bt-soft/pico-radio-5/doc/20250502_175417.jpg

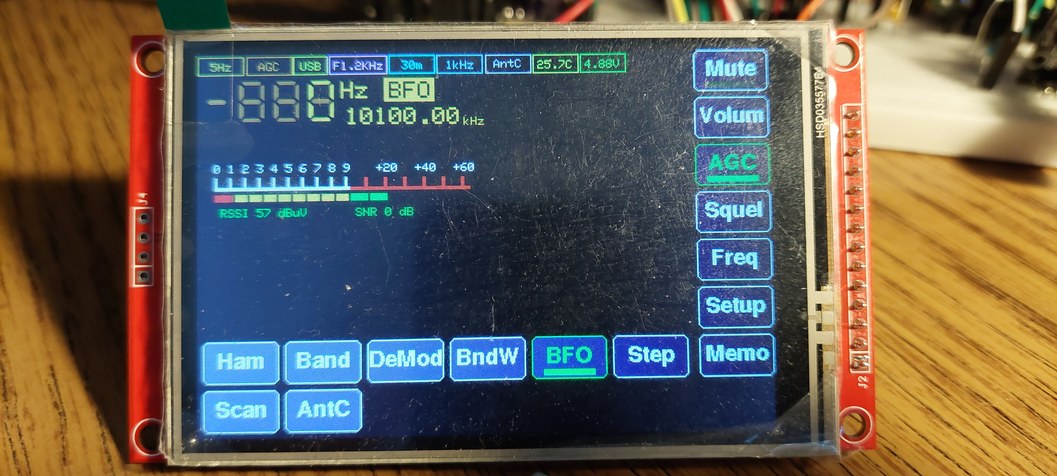
doc/20250502_175417.jpg
