bt-soft/pico-radio-5/doc/20250522_205130.jpg

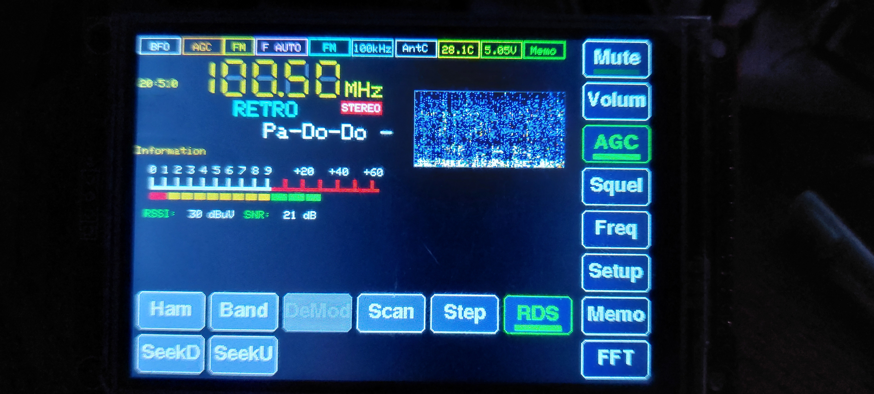
doc/20250522_205130.jpg
