bt-soft/pico-radio-5/doc/20250522_205135.jpg

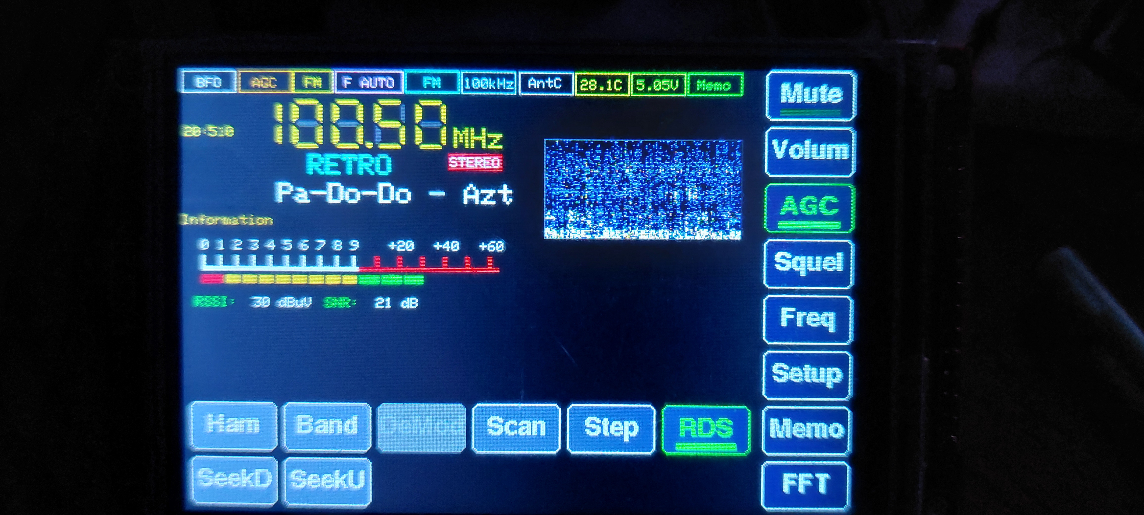
doc/20250522_205135.jpg
