bt-soft/pico-radio-5/doc/20250522_205156.jpg

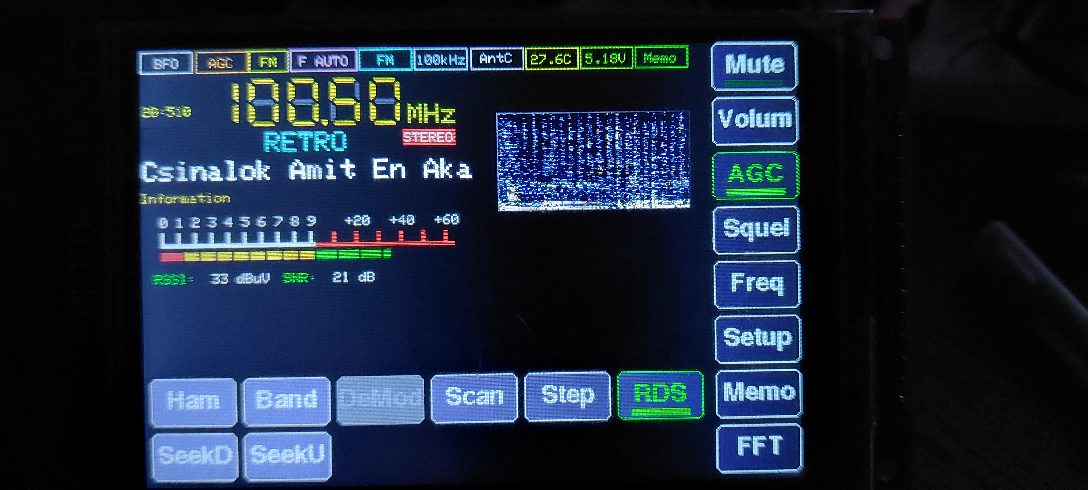
doc/20250522_205156.jpg
