bt-soft/pico-radio-5/doc/20250809_113343.jpg

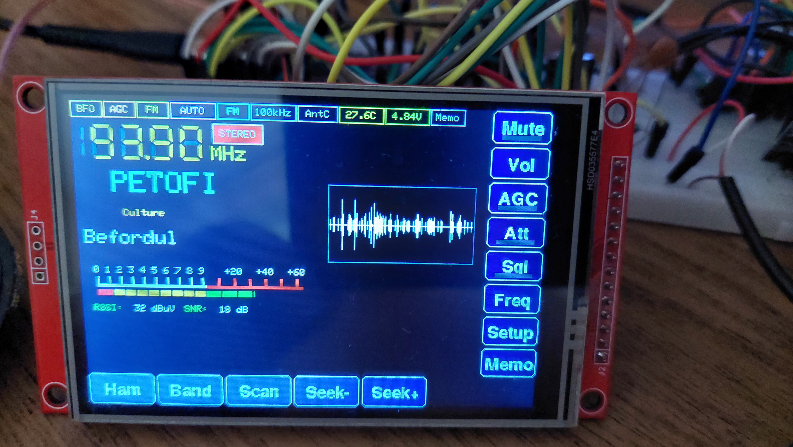
doc/20250809_113343.jpg
