bt-soft/pico-radio-5/include/DSEG7_Classic_Mini_Regular_34.h

// Created by http://oleddisplay.squix.ch/ Consider a donation
// In case of problems make sure that you are using the font file with the correct version!
const uint8_t DSEG7_Classic_Mini_Regular_34Bitmaps[] PROGMEM = {

    // Bitmap Data:
    0x00,                                                                                                                                                                         // ' '
    0x00,                                                                                                                                                                         // '!'
    0xFF, 0xA0, 0x28, 0x0A, 0x02, 0x80, 0xA0, 0x28, 0x0A, 0x02, 0x80, 0xA0, 0x28, 0x0A, 0x02, 0x80, 0xA0, 0x28, 0x0A, 0x02, 0x80, 0xA0, 0x28, 0x0A, 0x02, 0x80, 0xA0, 0x2F, 0xF8, // '"'
    0xFF, 0xA0, 0x28, 0x0A, 0x02, 0x80, 0xA0, 0x28, 0x0A, 0x02, 0x80, 0xA0, 0x28, 0x0A, 0x02, 0x80, 0xA0, 0x28, 0x0A, 0x02, 0x80, 0xA0, 0x28, 0x0A, 0x02, 0x80, 0xA0, 0x2F, 0xF8, // '#'
    0xFF, 0xA0, 0x28, 0x0A, 0x02, 0x80, 0xA0, 0x28, 0x0A, 0x02, 0x80, 0xA0, 0x28, 0x0A, 0x02, 0x80, 0xA0, 0x28, 0x0A, 0x02, 0x80, 0xA0, 0x28, 0x0A, 0x02, 0x80, 0xA0, 0x2F, 0xF8, // '$'
    0xFF, 0xA0, 0x28, 0x0A, 0x02, 0x80, 0xA0, 0x28, 0x0A, 0x02, 0x80, 0xA0, 0x28, 0x0A, 0x02, 0x80, 0xA0, 0x28, 0x0A, 0x02, 0x80, 0xA0, 0x28, 0x0A, 0x02, 0x80, 0xA0, 0x2F, 0xF8, // '%'
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
    {456, 4, 28, 29, 21, -31},  // '1'
    {470, 22, 34, 29, 3, -34},  // '2'
    {564, 19, 34, 29, 6, -34},  // '3'
    {645, 22, 28, 29, 3, -31},  // '4'
    {722, 22, 34, 29, 3, -34},  // '5'
    {816, 22, 34, 29, 3, -34},  // '6'
    {910, 22, 31, 29, 3, -34},  // '7'
    {996, 22, 34, 29, 3, -34},  // '8'
    {1090, 22, 34, 29, 3, -34}, // '9'
    {1184, 6, 19, 8, 1, -26},   // ':'
    {1199, 10, 23, 13, 1, -23}, // ';'
    {1228, 10, 23, 13, 1, -23}, // '<'
    {1257, 10, 23, 13, 1, -23}, // '='
    {1286, 10, 23, 13, 1, -23}, // '>'
    {1315, 10, 23, 13, 1, -23}, // '?'
    {1344, 10, 23, 13, 1, -23}, // '@'
    {1373, 22, 31, 29, 3, -34}, // 'A'
    {1459, 22, 31, 29, 3, -31}, // 'B'
    {1545, 20, 19, 29, 3, -19}, // 'C'
    {1593, 22, 31, 29, 3, -31}, // 'D'
    {1679, 20, 34, 29, 3, -34}, // 'E'
    {1764, 20, 31, 29, 3, -34}, // 'F'
    {1842, 22, 34, 29, 3, -34}, // 'G'
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
};
const GFXfont DSEG7_Classic_Mini_Regular_34 PROGMEM = {(uint8_t *)DSEG7_Classic_Mini_Regular_34Bitmaps, (GFXglyph *)DSEG7_Classic_Mini_Regular_34Glyphs, 0x20, 0x7E, 38};
