bt-soft/pico-radio-5/include/CommonVerticalButtons.h

#pragma once

#include "FrequencyInputDialog.h"
#include "ScreenRadioBase.h"
#include "Si4735Manager.h"
#include "UIButton.h"
#include "ValueChangeDialog.h"
#include "rtVars.h"

// ===================================================================
// UNIVERZÁLIS GOMB AZONOSÍTÓK - Egységes ID rendszer
// ===================================================================

namespace VerticalButtonIDs {
static constexpr uint8_t MUTE = 10;    ///< Némítás gomb (univerzális)
static constexpr uint8_t VOLUME = 11;  ///< Hangerő beállítás gomb (univerzális)
static constexpr uint8_t AGC = 12;     ///< Automatikus erősítés szabályozás (univerzális)
static constexpr uint8_t ATT = 13;     ///< Csillapító (univerzális)
static constexpr uint8_t SQUELCH = 14; ///< Zajzár beállítás (univerzális)
static constexpr uint8_t FREQ = 15;    ///< Frekvencia input (univerzális)
static constexpr uint8_t SETUP = 16;   ///< Beállítások képernyő (univerzális)
static constexpr uint8_t MEMO = 17;    ///< Memória funkciók (univerzális)
} // namespace VerticalButtonIDs

/**
 * @brief Közös függőleges gombsor statikus osztály dialógus támogatással
 * @details Handler függvények képesek dialógusokat megjeleníteni
 */
class CommonVerticalButtons {
  public:
    // =====================================================================
    // HANDLER FÜGGVÉNY TÍPUSOK - Egységes ScreenRadioBase alapú megközelítés
    // =====================================================================
    using HandlerFunc = void (*)(const UIButton::ButtonEvent &, ScreenRadioBase *);

    // Kompatibilitás miatt megtartjuk a régi neveket, de mind azonos típusra mutatnak
    using CommonHandlerFunc = HandlerFunc;
    using Si4735HandlerFunc = HandlerFunc;
    using DialogHandlerFunc = HandlerFunc;

    /**
     * @brief Gomb statikus adatok struktúrája
     */
    struct ButtonDefinition {
        uint8_t id;                         ///< Gomb azonosító
        const char *label;                  ///< Gomb felirata
        UIButton::ButtonType type;          ///< Gomb típusa
        UIButton::ButtonState initialState; ///< Kezdeti állapot
        uint16_t height;                    ///< Gomb magassága
        HandlerFunc handler;                ///< Egységes handler függvény
    };

    // =====================================================================
    // UNIVERZÁLIS GOMBKEZELŐ METÓDUSOK - Dialógus támogatással
    // =====================================================================

    /**
     * @brief Segédmetódus gombállapot frissítéséhez ScreenRadioBase-en keresztül (RTTI-mentes)
     */
    static void updateButtonStateInScreen(ScreenRadioBase *screen, uint8_t buttonId, UIButton::ButtonState state) {
        if (!screen)
            return;

        // Vegigmegyünk a screen összes gyerek komponensén
        auto &components = screen->getChildren();
        for (auto &component : components) {

            // Próbáljuk meg UIButton-ként kezelni (raw pointer cast)
            UIButton *button = reinterpret_cast<UIButton *>(component.get());

            // Ellenőrizzük, hogy valóban UIButton-e az ID alapján
            // (Az UIButton ID-k a VerticalButtonIDs tartományban vannak)
            if (button && button->getId() == buttonId) {
                button->setButtonState(state);
                break;
            }
        }
    }

    /**
     * @brief MUTE gomb kezelő
     */
    static void handleMuteButton(const UIButton::ButtonEvent &event, ScreenRadioBase *screen = nullptr) {
        if (event.state != UIButton::EventButtonState::On && event.state != UIButton::EventButtonState::Off) {
            return;
        }
        rtv::muteStat = event.state == UIButton::EventButtonState::On;
        ::pSi4735Manager->getSi4735().setAudioMute(rtv::muteStat);
    }
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
